MastaTabs/a500spwr/pix/IMG_20200426_200057_s.jpg

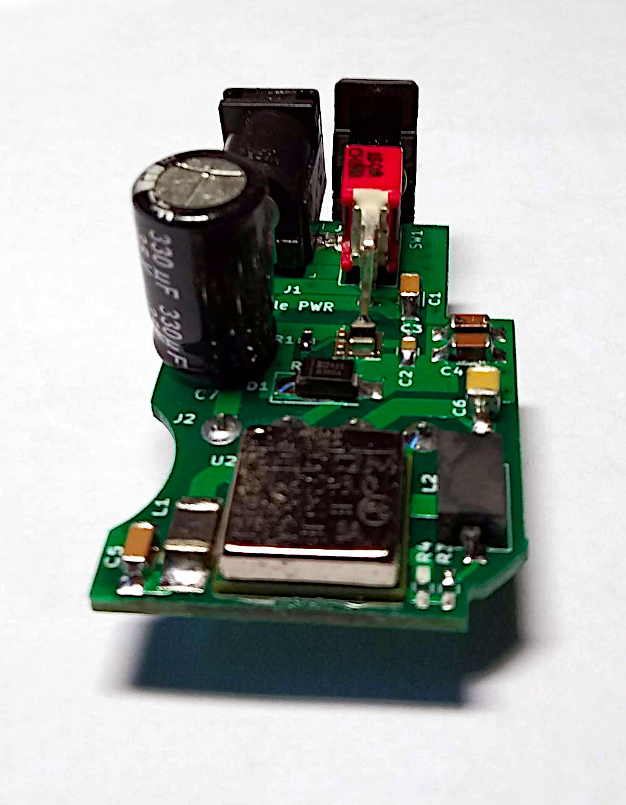
pix/IMG_20200426_200057_s.jpg
