MastaTabs/a500spwr/pix/IMG_20200426_200154_s.jpg

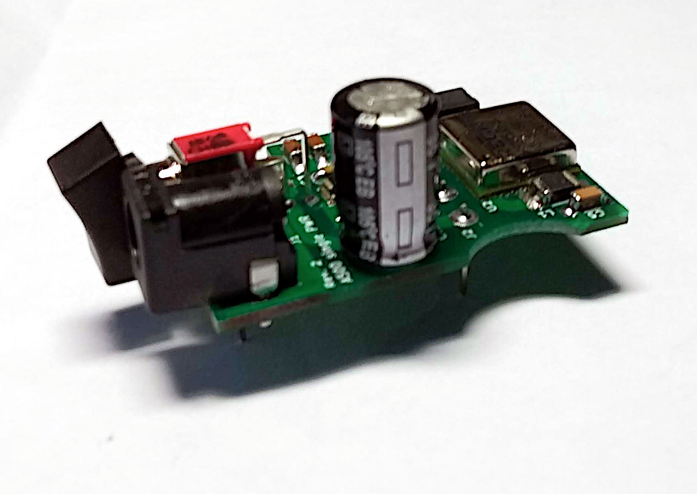
pix/IMG_20200426_200154_s.jpg
